MikeMontana1968/esp32-eInk-Lidar/src/classes/MyTask.cpp

#pragma once
#include "freertos/FreeRTOS.h"
#include "freertos/task.h"

// https://saludpcb.com/learn-c-inheritance-with-esp32-powerful-task-setup/

class MyTask {
public:
    MyTask(const char* name, uint32_t stackSize, UBaseType_t priority)
        : taskName(name), taskStackSize(stackSize), taskPriority(priority), taskHandle(nullptr) {}

    void start() {
        xTaskCreate(taskFunctionWrapper, taskName, taskStackSize, this, taskPriority, &taskHandle);
    }

protected:
    virtual void run() = 0;

private:
    static void taskFunctionWrapper(void* parameter) {
        MyTask* task = static_cast<MyTask*>(parameter);
        task->run();
    }

    const char* taskName;
    uint32_t taskStackSize;
    UBaseType_t taskPriority;
    TaskHandle_t taskHandle;
};
